Freimor/CUSTOM-IMAC27-monitor-with-R1820/images/camera_replacement.jpg

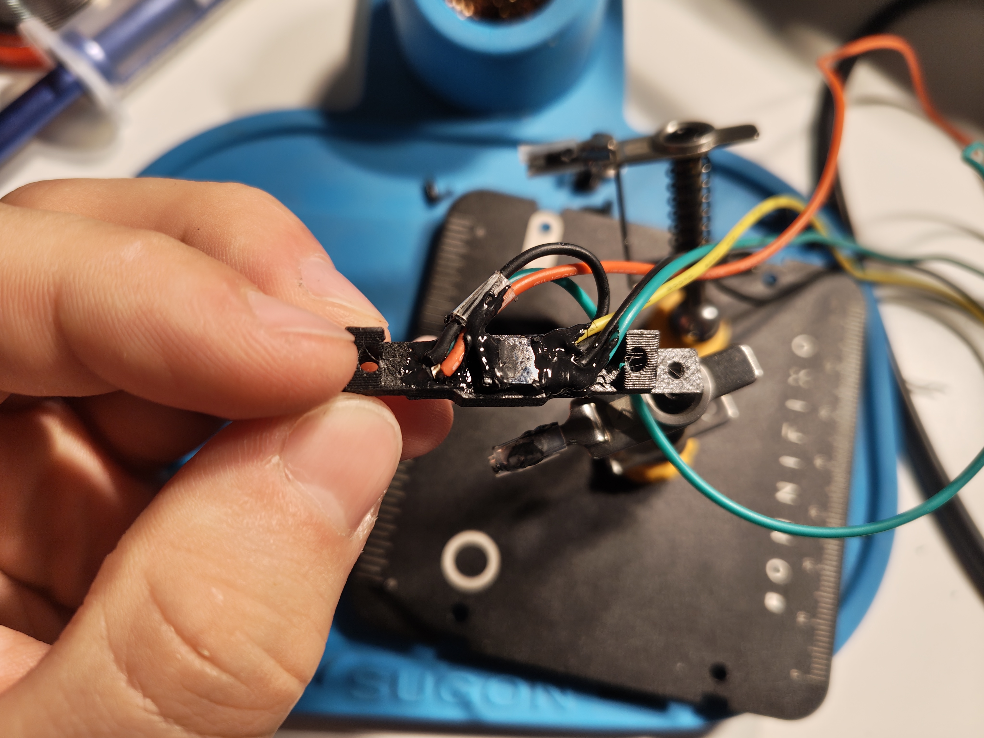
images/camera_replacement.jpg
